Kllngii/Wetterstation/slint-pico/src/main.rs

#![no_std]
#![cfg_attr(not(feature = "simulator"), no_main)]
#![crate_name = "slint_pico"]
//#![feature(type_alias_impl_trait)]
//#![feature(async_fn_in_trait)]


#[cfg(feature = "panic-probe")]
extern crate defmt_rtt;
#[cfg(feature = "panic-probe")]
extern crate panic_probe;
extern crate alloc;

#[cfg(feature = "simulator")]
mod simulator_support;

#[cfg(not(feature = "simulator"))]
mod xpt2046;
#[cfg(not(feature = "simulator"))]
mod pico_backend;

#[cfg(not(feature = "simulator"))]
mod meteotime;

#[cfg(not(feature = "simulator"))]
mod display_interface_spi;

slint::include_modules!();

fn create_slint_app() -> AppWindow {
    AppWindow::new().expect("Failed to load UI")
}

#[cfg_attr(not(feature = "simulator"), rp_pico::entry)]
fn main() -> ! {

    #[cfg(not(feature = "simulator"))] {
        pico_backend::init();

        let ui = create_slint_app();
        let _timer = pico_backend::init_timers(ui.as_weak());
        ui.run().unwrap();
        core::panic!("Kann eigentlich nicht vorkommen...");
    }

    #[cfg(feature = "simulator")]
    uc_support::uc_main();
}
