Kllngii/Wetterstation/slint-pico/src/xpt2046.rs

/*! Dieses `XPT2046` Modul kümmert sich um die Ansteuerung und Auswertung der Touch-Inputs des Users

    Basiert auf dem Beispiel der SixtyFPS GmbH <info@slint.dev>
 */
use core::cell::RefCell;
use cortex_m::interrupt::Mutex;
use defmt::{info, warn};
use embedded_hal::blocking::spi::Transfer;
use embedded_hal::digital::v2::{InputPin, OutputPin};
use euclid::default::Point2D;
use fugit::Hertz;
use st7789::Orientation;

#[cfg(feature = "panic-probe")]
extern crate defmt_rtt;
#[cfg(feature = "panic-probe")]
extern crate panic_probe;

pub const SPI_FREQ: Hertz<u32> = Hertz::<u32>::Hz(3_000_000);

pub struct XPT2046<IRQ: InputPin + 'static, CS: OutputPin, SPI: Transfer<u8>> {
    irq: &'static Mutex<RefCell<Option<IRQ>>>,
    cs: CS,
    spi: SPI,
    orientation: Orientation,
    pressed: bool,
}

impl<PinE, IRQ: InputPin<Error = PinE>, CS: OutputPin<Error = PinE>, SPI: Transfer<u8>>
XPT2046<IRQ, CS, SPI>
{
    pub fn new(
        irq: &'static Mutex<RefCell<Option<IRQ>>>,
        mut cs: CS,
        spi: SPI,
        orientation: Orientation
    ) -> Result<Self, PinE> {
        cs.set_high()?;
        Ok(Self { irq, cs, spi, orientation, pressed: false })
    }

    pub fn read(&mut self) -> Result<Option<Point2D<f32>>, Error<PinE, SPI::Error>> {
        const PRESS_THRESHOLD: i32 = -25_000;
        const RELEASE_THRESHOLD: i32 = -30_000;
        let threshold = if self.pressed { RELEASE_THRESHOLD } else { PRESS_THRESHOLD };
        self.pressed = false;

        if cortex_m::interrupt::free(|cs| {
            self.irq.borrow(cs).borrow().as_ref().unwrap().is_low()
        })
            .map_err(|e| Error::Pin(e))?
        {
            const CMD_X_READ: u8 = 0b10010000;
            const CMD_Y_READ: u8 = 0b11010000;
            const CMD_Z1_READ: u8 = 0b10110000;
            const CMD_Z2_READ: u8 = 0b11000000;

            // These numbers were measured approximately.
            const MIN_X: u32 = 1900;
            const MAX_X: u32 = 30300;
            const MIN_Y: u32 = 2300;
            const MAX_Y: u32 = 30300;

            self.cs.set_low().map_err(|e| Error::Pin(e))?;

            macro_rules! xchg {
                ($byte:expr) => {
                    match self
                        .spi
                        .transfer(&mut [$byte, 0, 0])
                        .map_err(|e| Error::Transfer(e))?
                    {
                        [_, h, l] => ((*h as u32) << 8) | (*l as u32),
                        _ => return Err(Error::InternalError),
                    }
                };
            }

            let z1 = xchg!(CMD_Z1_READ);
            let z2 = xchg!(CMD_Z2_READ);
            let z = z1 as i32 - z2 as i32;

            if z < threshold {
                xchg!(0);
                self.cs.set_high().map_err(|e| Error::Pin(e))?;
                return Ok(None);
            }

            xchg!(CMD_X_READ | 1); // Dummy read, first read is a outlier

            let mut point = Point2D::new(0u32, 0u32);
            for _ in 0..10 {
                let y = xchg!(CMD_Y_READ);
                let x = xchg!(CMD_X_READ);
                point += euclid::vec2(i16::MAX as u32 - x, y)
            }

            let z1 = xchg!(CMD_Z1_READ);
            let z2 = xchg!(CMD_Z2_READ);
            let z = z1 as i32 - z2 as i32;

            xchg!(0);
            self.cs.set_high().map_err(|e| Error::Pin(e))?;

            if z < RELEASE_THRESHOLD {
                return Ok(None);
            }

            point /= 10;
            self.pressed = true;
            match self.orientation {
                Orientation::LandscapeSwapped => {
                    Ok(Some(euclid::point2(
                        1f32 - (point.x.saturating_sub(MIN_X) as f32 / (MAX_X - MIN_X) as f32),
                        1f32 - (point.y.saturating_sub(MIN_Y) as f32 / (MAX_Y - MIN_Y) as f32),
                    )))
                }
                Orientation::Landscape => {
                    Ok(Some(euclid::point2(
                        point.x.saturating_sub(MIN_X) as f32 / (MAX_X - MIN_X) as f32,
                        point.y.saturating_sub(MIN_Y) as f32 / (MAX_Y - MIN_Y) as f32,
                    )))
                }
                _ => {
                    warn!("Touch für diese Ausrichtung noch nicht implementiert!");
                    Ok(None)
                }
            }

        } else {
            Ok(None)
        }
    }
}

pub enum Error<PinE, TransferE> {
    Pin(PinE),
    Transfer(TransferE),
    InternalError,
}
