Kllngii/Wetterstation/externalSensor_nano/DataTypes.h

/*
 *  Created by: faschmali
 *
 *  Here are all relevant definitions of structs used for communication
 *  between the microcontrollers. The structs are used as part of a union
 *  to be able to send all elements bytewise. The pragma is needed to avoid
 *  padding bytes that increase the size of the structs and make a checksum
 *  calculation more complicated. 
 */

#ifndef DATATYPES_H_
#define DATATYPES_H_

#include <stdint.h>

#pragma pack(push,1)
typedef struct {
    const char dataType[4];
    uint8_t hour;
    uint8_t minute;
    uint8_t second;
    uint16_t year;
    uint8_t month;
    uint8_t day;
    uint8_t weekDay;
    uint8_t checksum;
} TimeStruct;
#pragma pack(pop)

typedef union {
    char buf[sizeof(TimeStruct)];
    TimeStruct data;
} TimeSendBuf;

#pragma pack(push,1)
typedef struct {
    char dataType[4];
    float temp;
    float humidity;
    float pressure;
    uint8_t checksum;
} BMEStruct;
#pragma pack(pop)

typedef union {
    char buf[sizeof(BMEStruct)];
    BMEStruct data;
} BMESendBuf;

#endif /* DATATYPES_H */
